fra589/BeCG/images/Screenshot_captiveportal.jpg

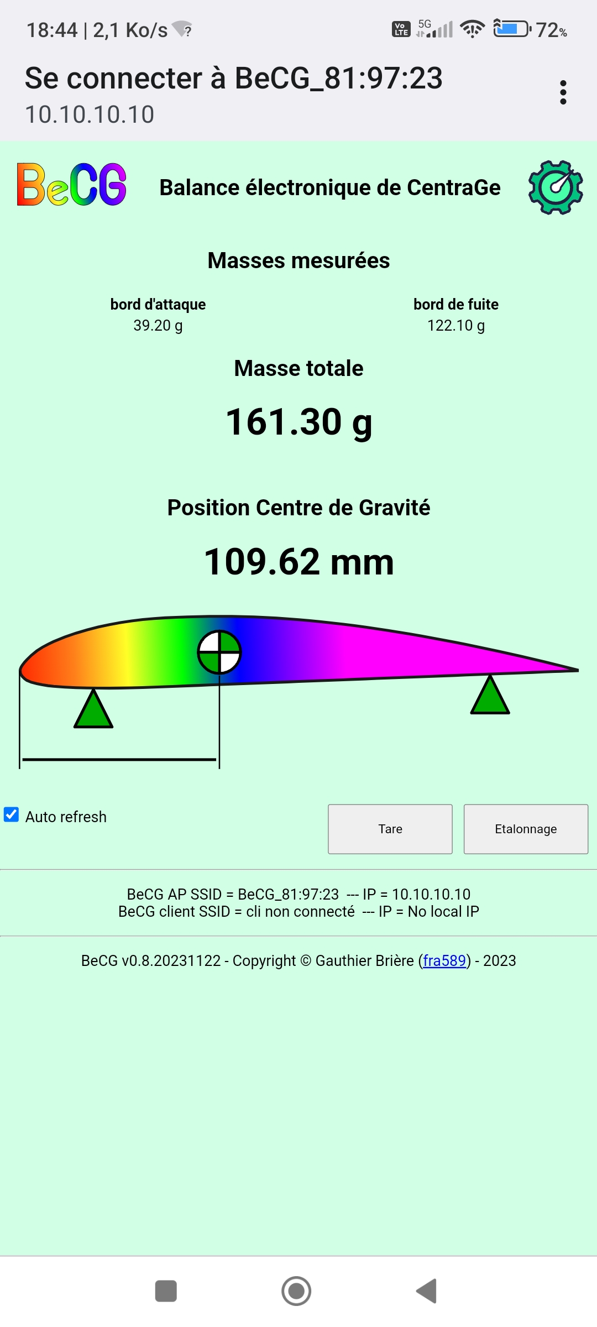
images/Screenshot_captiveportal.jpg
