fra589/BeCG/freecad/balanceCentrage01-entretoise.stl

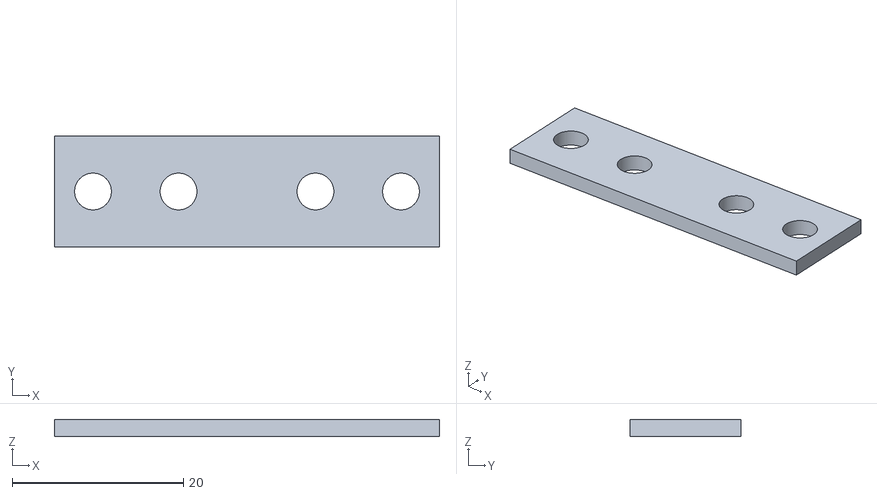
[picture p24: CAD file, 2023-11-23]
freecad/balanceCentrage01-entretoise.stl
45.0 x 13.0 x 2.00
