fra589/BeCG/freecad/balanceCentrage01-boutonTare.stl

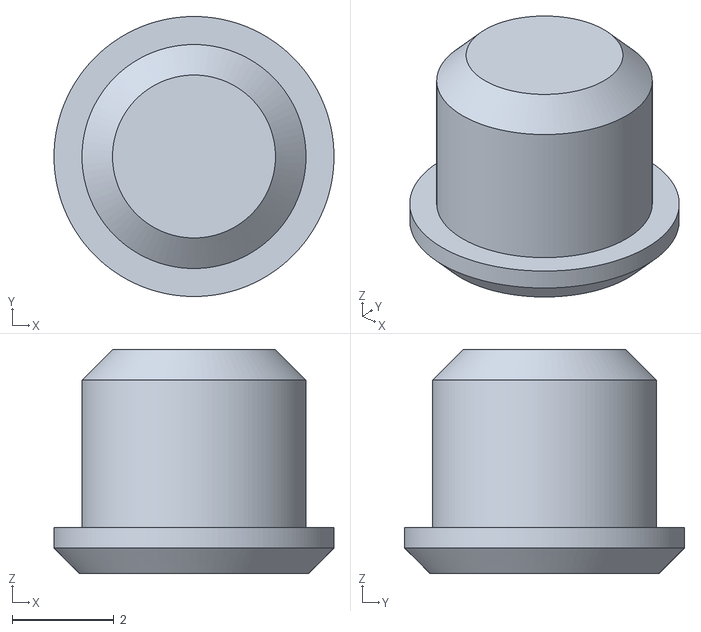
[picture p25: CAD file, 2023-11-23]
freecad/balanceCentrage01-boutonTare.stl
5.50 x 5.50 x 4.40
