fra589/BeCG/freecad/balanceCentrage01-clipFilsCourt.stl

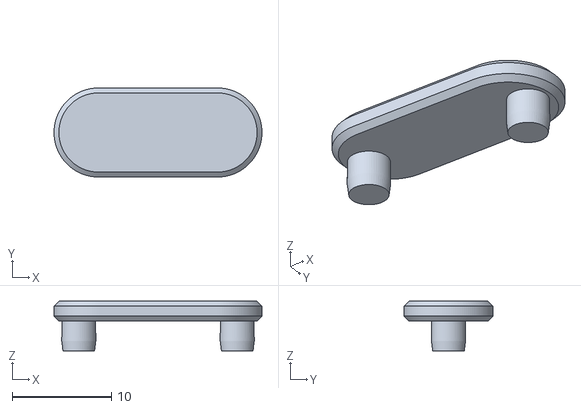
[picture p26: CAD file, 2023-11-23]
freecad/balanceCentrage01-clipFilsCourt.stl
21.0 x 9.00 x 5.00
