fra589/BeCG/BeCG/bitmaps.h

/****************************************************************************/
/*                                                                          */
/* Copyright (C) 2023-2024 Gauthier Brière (gauthier.briere "at" gmail.com) */
/*                                                                          */
/* This file: bitmaps.h is part of BeCG                                     */
/*                                                                          */
/* BeCG is free software: you can redistribute it and/or modify it          */
/* under the terms of the GNU General Public License as published by        */
/* the Free Software Foundation, either version 3 of the License, or        */
/* (at your option) any later version.                                      */
/*                                                                          */
/* BeCG is distributed in the hope that it will be useful, but              */
/* WITHOUT ANY WARRANTY; without even the implied warranty of               */
/* MERCHANTABILITY or FITNESS FOR A PARTICULAR PURPOSE.  See the            */
/* GNU General Public License for more details.                             */
/*                                                                          */
/* You should have received a copy of the GNU General Public License        */
/* along with this program.  If not, see <http://www.gnu.org/licenses/>.    */
/*                                                                          */
/****************************************************************************/

#define BeCG_splash_width  128
#define BeCG_splash_height 64
#define copyright_width  12
#define copyright_height 16

static const uint8_t PROGMEM BeCG_splash[] = {
  0b00000000,0b00000000,0b00000000,0b00000000,0b00000000,0b00000000,0b00000000,0b00000000,0b00000000,0b00000000,0b00000000,0b00000000,0b00000000,0b00000000,0b00000000,0b00000000,
  0b00000011,0b11111111,0b11111111,0b11000000,0b00000000,0b00000000,0b00000000,0b00000000,0b00000000,0b00111111,0b00000000,0b00000000,0b00000000,0b01111110,0b00000000,0b00000000,
  0b00000011,0b11111111,0b11111111,0b11110000,0b00000000,0b00000000,0b00000000,0b00000000,0b00000001,0b11111111,0b11100000,0b00000000,0b00000011,0b11111111,0b11000000,0b00000000,
  0b00000011,0b11111111,0b11111111,0b11111100,0b00000000,0b00000000,0b00000000,0b00000000,0b00000011,0b11111111,0b11110000,0b00000000,0b00000111,0b11111111,0b11100000,0b00000000,
  0b00000011,0b11111111,0b11111111,0b11111110,0b00000000,0b00000000,0b00000000,0b00000000,0b00001111,0b11111111,0b11111100,0b00000000,0b00011111,0b11111111,0b11111000,0b00000000,
  0b00000011,0b11111111,0b11111111,0b11111111,0b00000000,0b00000000,0b00000000,0b00000000,0b00011111,0b11111111,0b11111110,0b00000000,0b00111111,0b11111111,0b11111100,0b00000000,
  0b00000011,0b11111111,0b11111111,0b11111111,0b10000000,0b00000000,0b00000000,0b00000000,0b00111111,0b11111111,0b11111110,0b00000000,0b01111111,0b11111111,0b11111100,0b00000000,
  0b00000011,0b11111111,0b11111111,0b11111111,0b10000000,0b00000000,0b00000000,0b00000000,0b00111111,0b11111111,0b11111111,0b00000000,0b01111111,0b11111111,0b11111110,0b00000000,
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
  0b10010000,0b10010000,
  0b10110000,0b00010000,
  0b10110000,0b00010000,
  0b10110000,0b00010000,
  0b10110000,0b00010000,
  0b10010000,0b10010000,
  0b01011111,0b10100000,
  0b01101111,0b01100000,
  0b00110000,0b11000000,
  0b00001111,0b00000000,
  0b00000000,0b00000000,
};
